ksarkies/XBee-Acquisition/Documentation/Kicad-main-sch.png

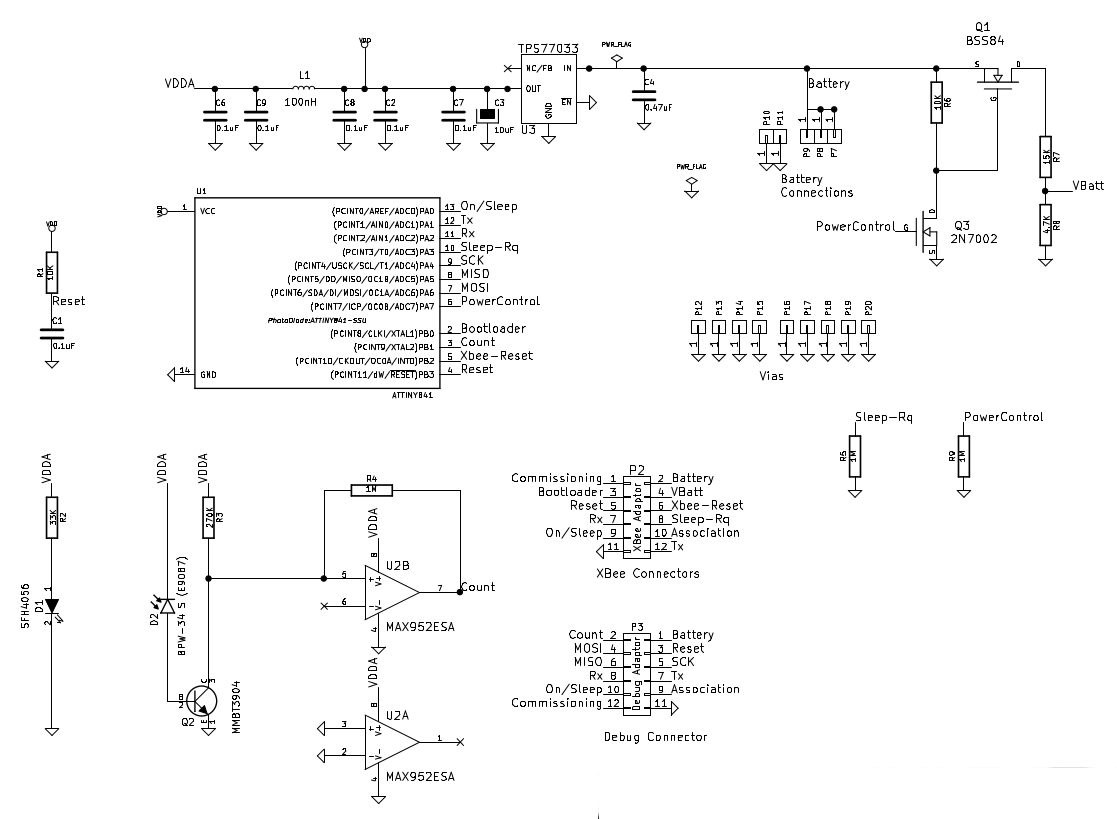
Documentation/Kicad-main-sch.png
