ksarkies/XBee-Acquisition/Documentation/Kicad-mounts-pcb-v4.png

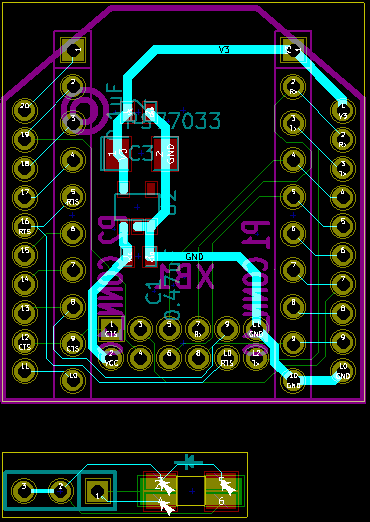
Documentation/Kicad-mounts-pcb-v4.png
