ksarkies/XBee-Acquisition/Documentation/Kicad-mounts-pcb.jpg

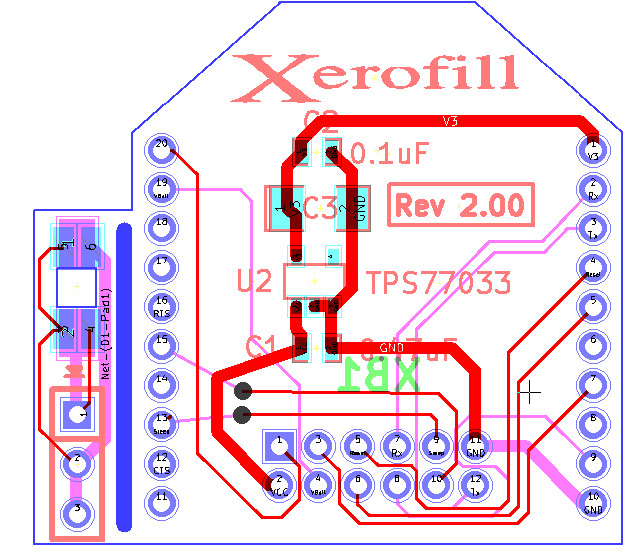
Documentation/Kicad-mounts-pcb.jpg
