ksarkies/XBee-Acquisition/Documentation/Kicad-mounts-sch.png

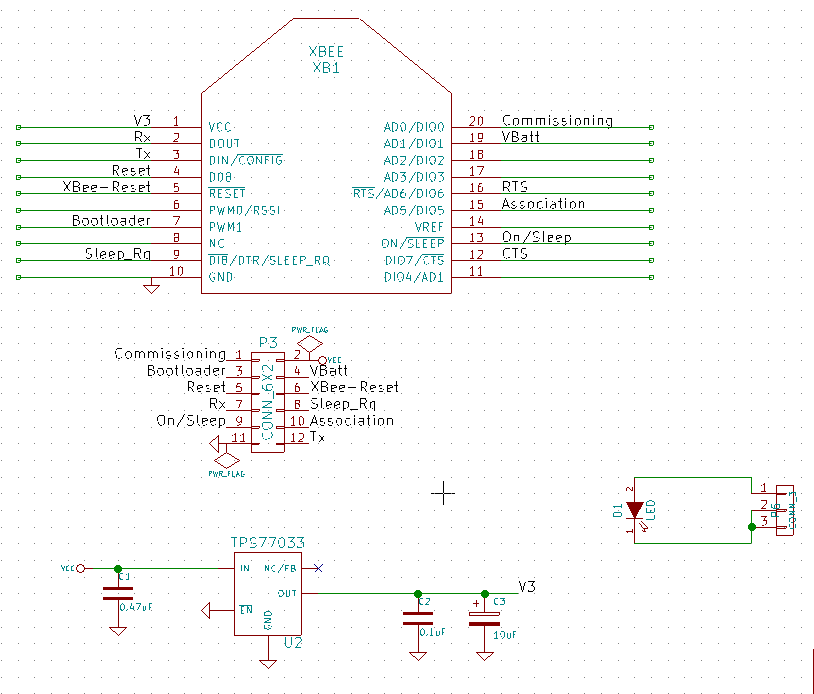
Documentation/Kicad-mounts-sch.png
