ksarkies/XBee-Acquisition/Documentation/LED-mounting-angle.jpg

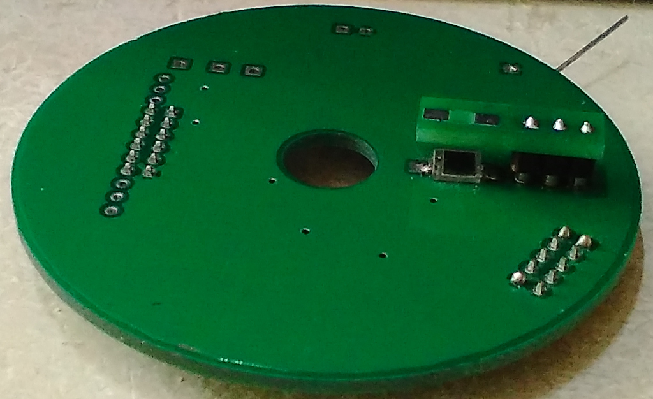
Documentation/LED-mounting-angle.jpg
