ksarkies/XBee-Acquisition/Documentation/LED-mounting-apart.jpg

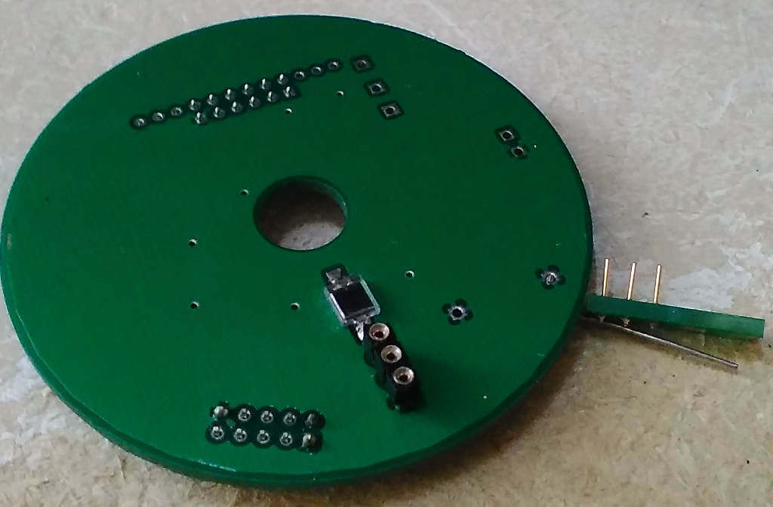
Documentation/LED-mounting-apart.jpg
