ksarkies/XBee-Acquisition/Documentation/network.png

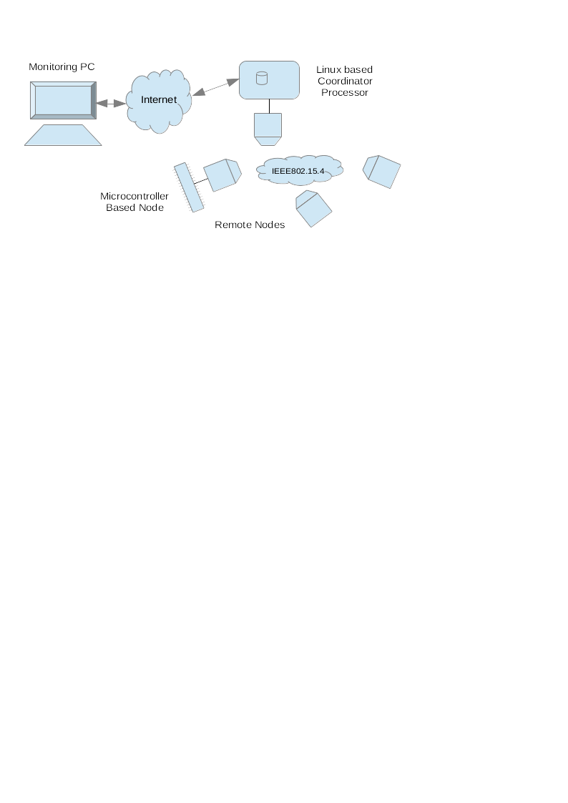
Documentation/network.png
