ksarkies/XBee-Acquisition/Documentation/Topside-of-Meter-Board-v2.jpg

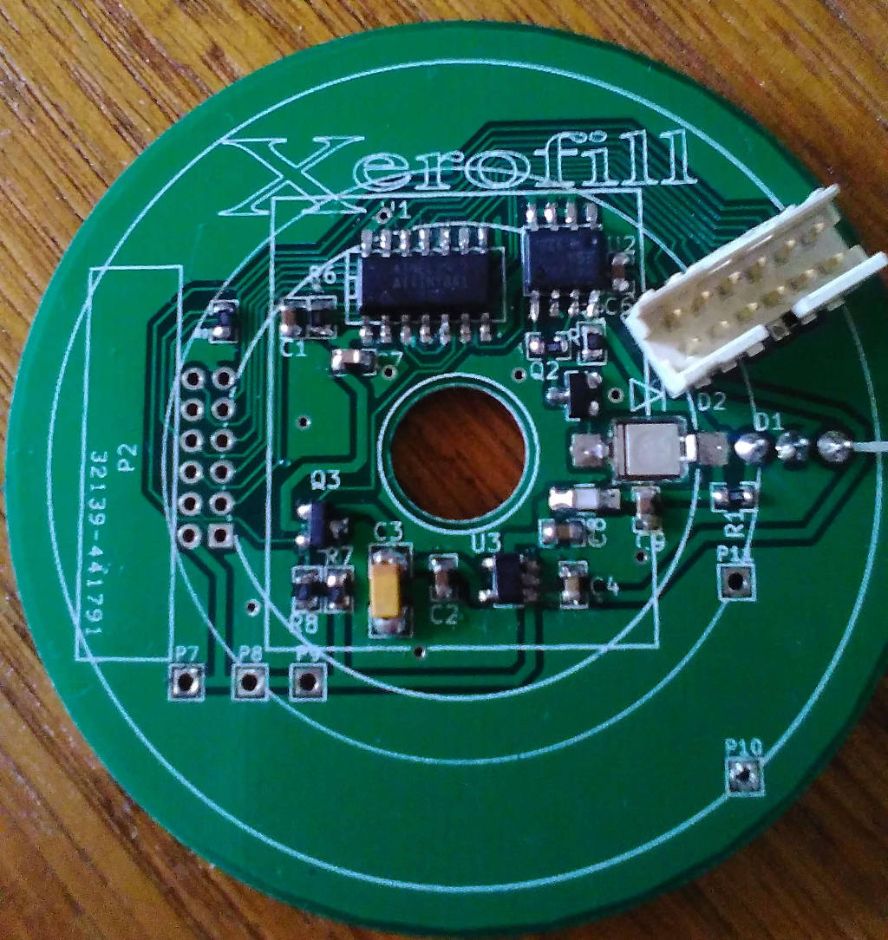
Documentation/Topside-of-Meter-Board-v2.jpg
