ksarkies/XBee-Acquisition/Documentation/Topside-of-Mounts-Board-v2.jpg

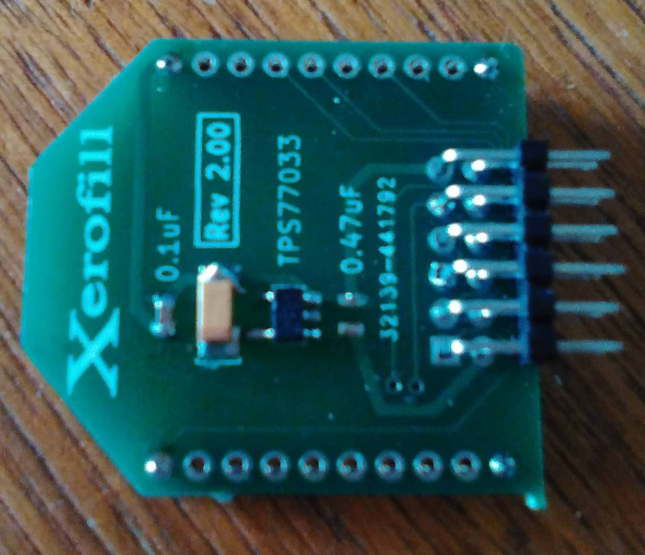
Documentation/Topside-of-Mounts-Board-v2.jpg
