ksarkies/XBee-Acquisition/Documentation/XBee-mount-bottom-view-1.jpg

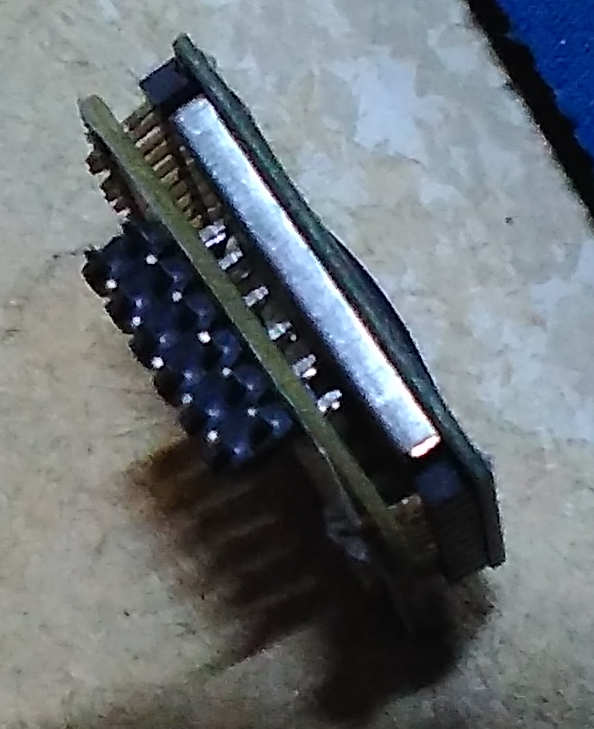
Documentation/XBee-mount-bottom-view-1.jpg
