ksarkies/XBee-Acquisition/Documentation/XBee-mount-bottom-view-2.jpg

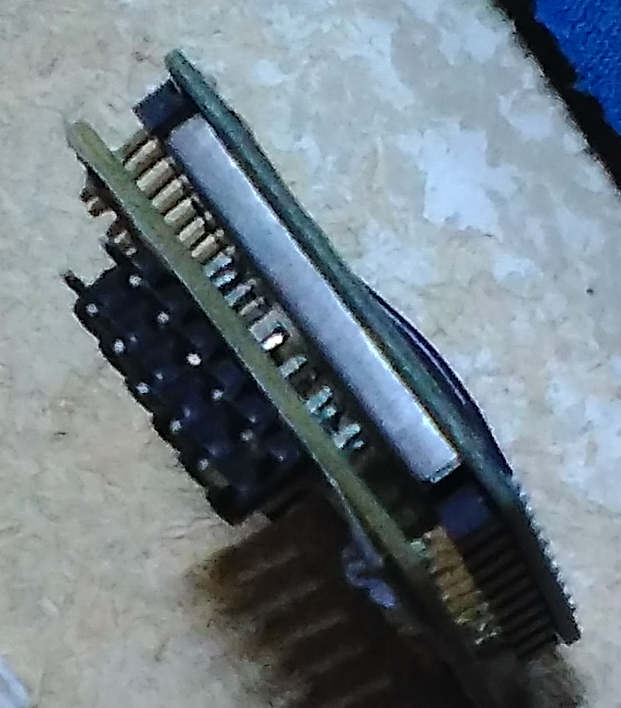
Documentation/XBee-mount-bottom-view-2.jpg
