ksarkies/XBee-Acquisition/Documentation/XBee-mount-side-view.jpg

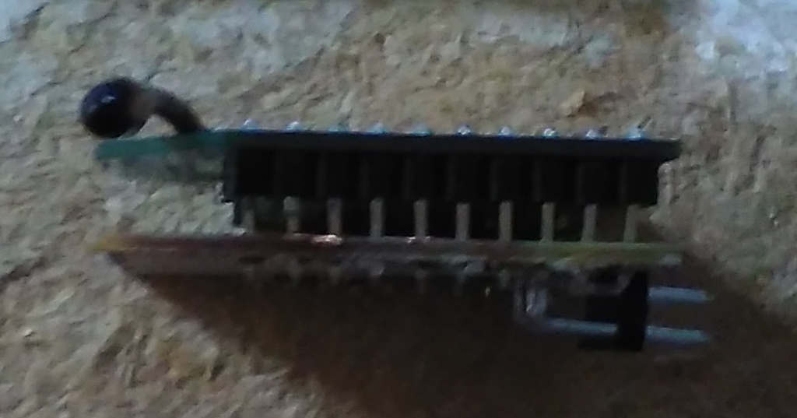
Documentation/XBee-mount-side-view.jpg
