ksarkies/XBee-Acquisition/Development/gEDA-XBee-node-test/xbee-node-atmega48.png

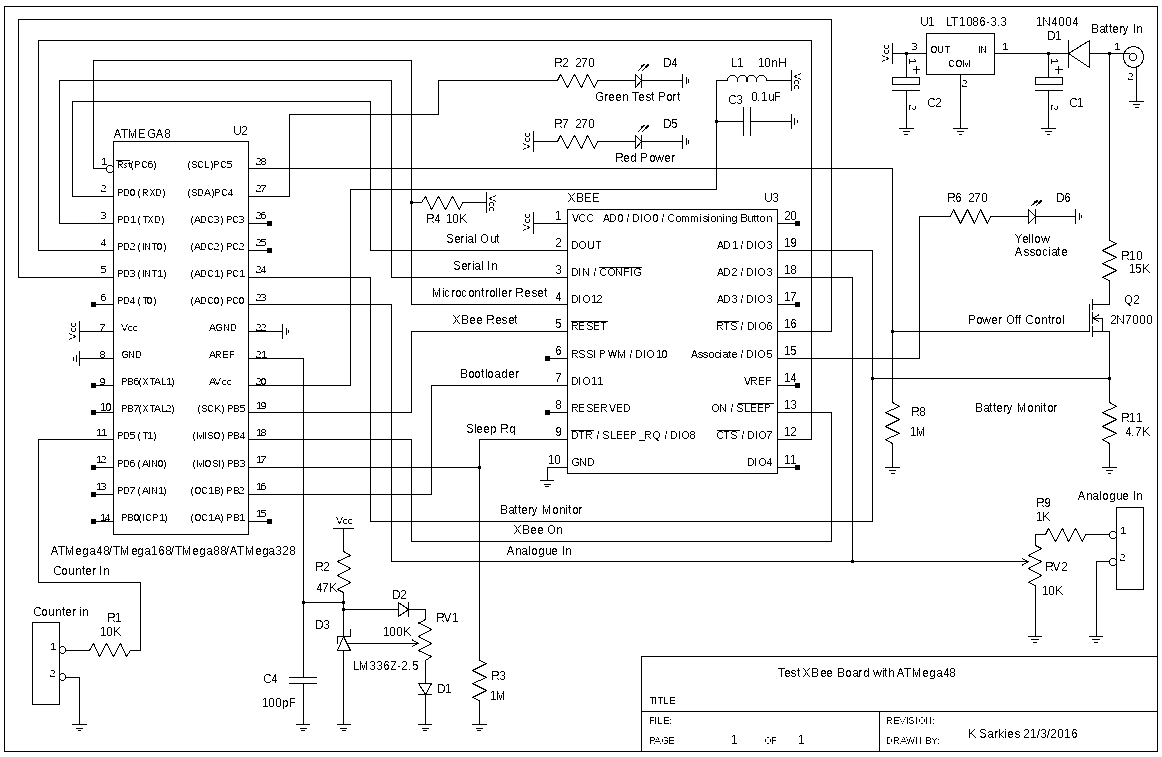
Development/gEDA-XBee-node-test/xbee-node-atmega48.png
