ksarkies/XBee-Acquisition/Development/gEDA-XBee-node-test/xbee-node-attiny4313.png

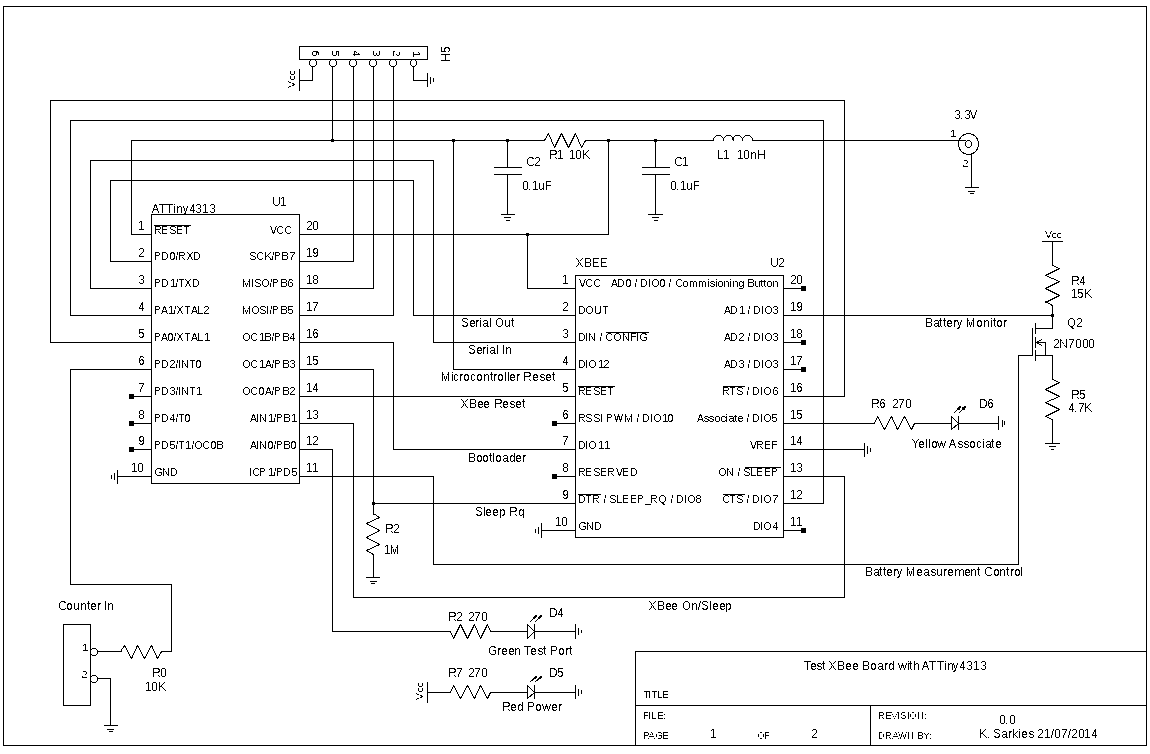
Development/gEDA-XBee-node-test/xbee-node-attiny4313.png
