ksarkies/XBee-Acquisition/Development/gEDA-XBee-node-test/xbee-node-serial.png

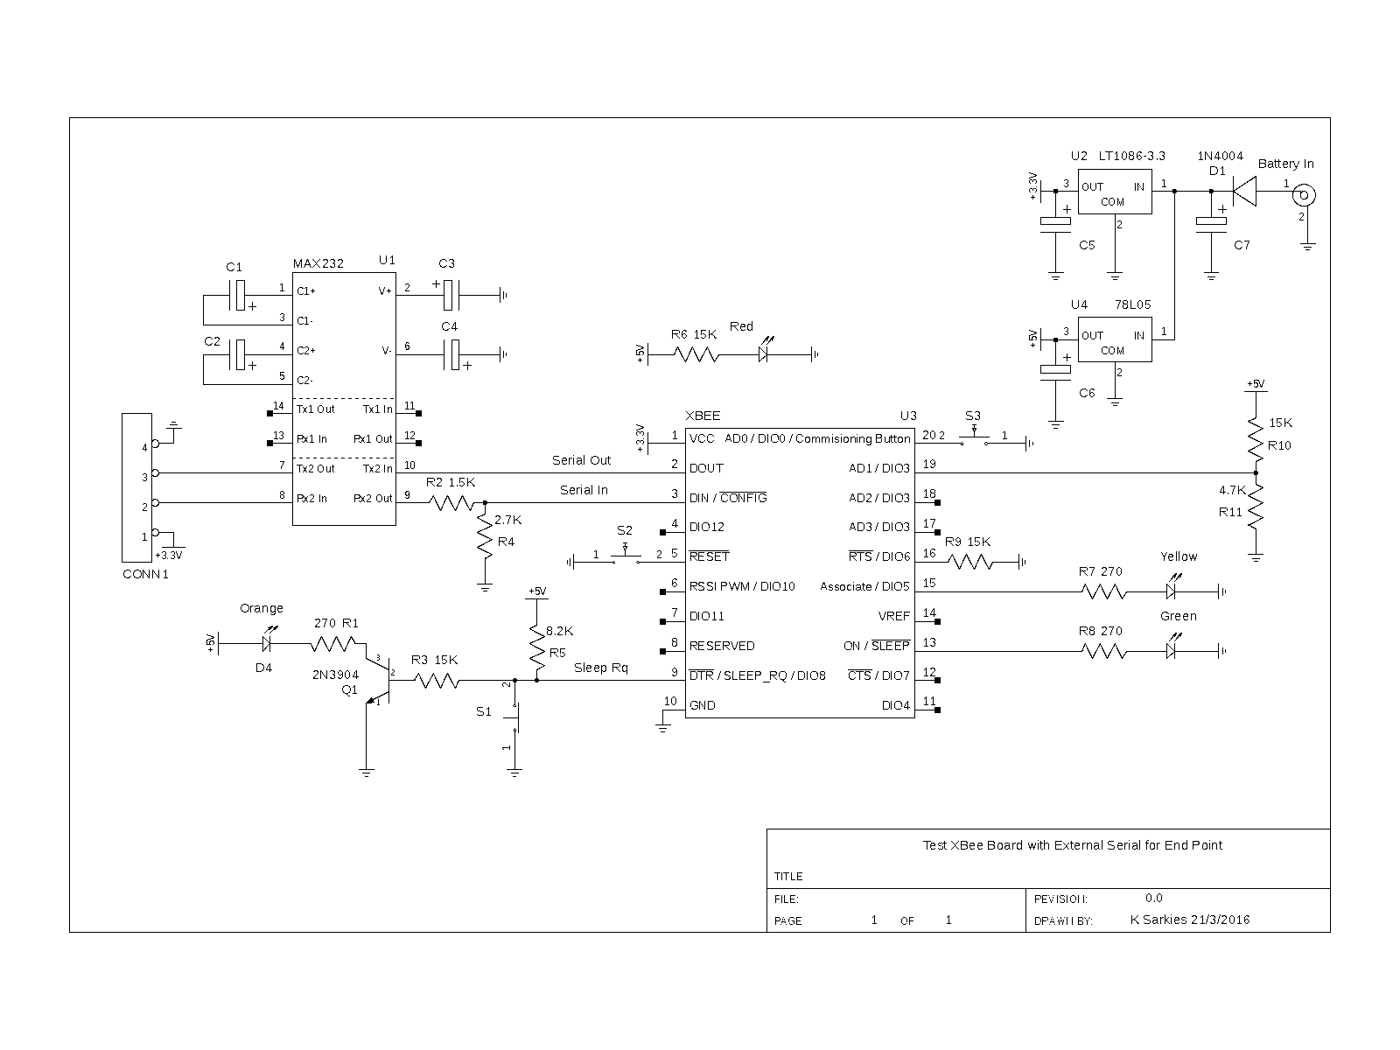
Development/gEDA-XBee-node-test/xbee-node-serial.png
