ksarkies/XBee-Acquisition/Development/Kicad-XBee-node-test/xbee-node-test.jpg

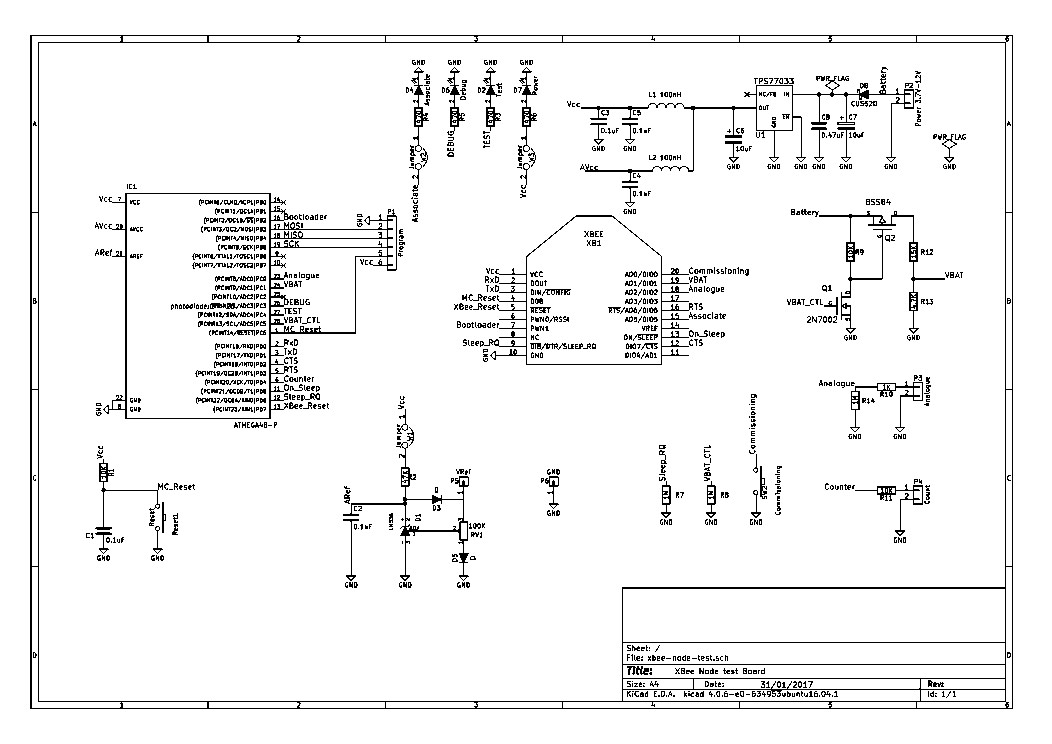
Development/Kicad-XBee-node-test/xbee-node-test.jpg
