ksarkies/XBee-Acquisition/Documentation/Kicad-TestBoard-pcb-v2.jpg

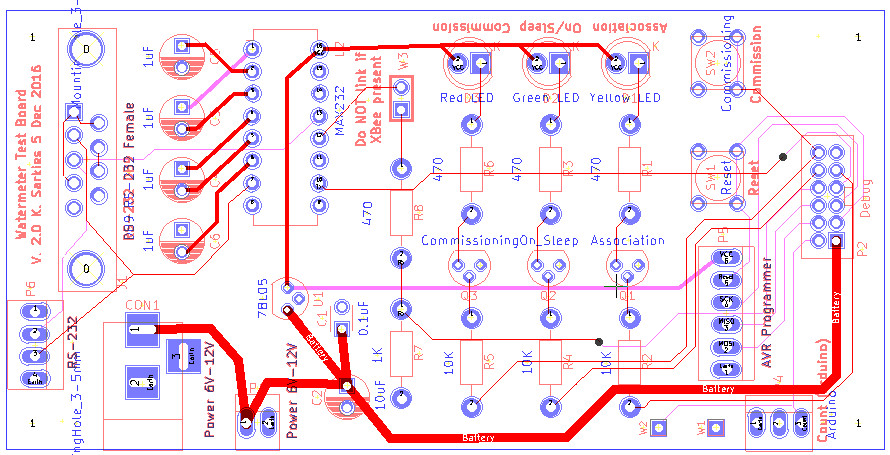
Documentation/Kicad-TestBoard-pcb-v2.jpg
