ksarkies/XBee-Acquisition/Documentation/Kicad-TestBoard-sch-v2.jpg

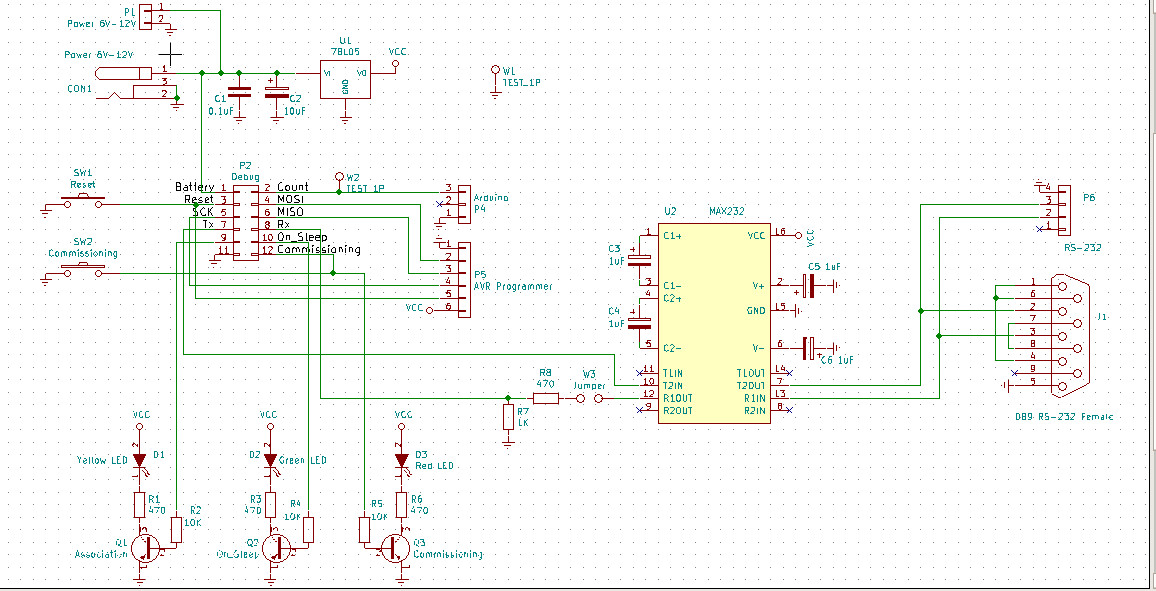
Documentation/Kicad-TestBoard-sch-v2.jpg
