ksarkies/XBee-Acquisition/Documentation/Topside-of-Testboard-v1.jpg

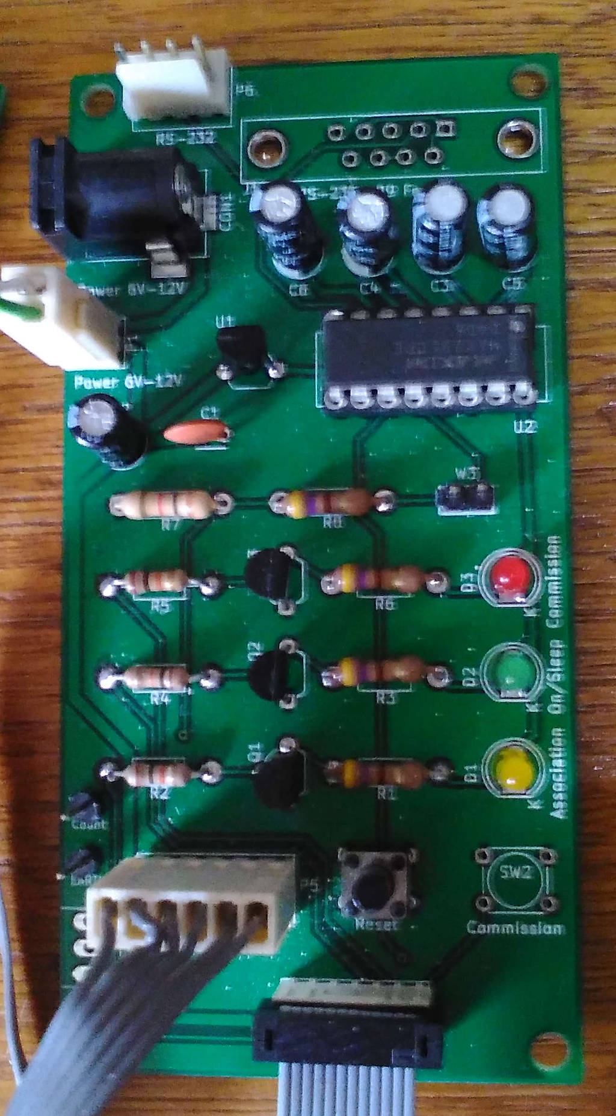
Documentation/Topside-of-Testboard-v1.jpg
