ksarkies/XBee-Acquisition/XBee-firmware/xbee-avr.c

/**
@mainpage XBee AVR Node Unit
@version 0.0.0
@author Ken Sarkies (www.jiggerjuice.info)
@date 4 January 2013
@brief Code for an AVR with an XBee in a Remote Low Power Node

This code forms the core of an interface between an XBee networking device
using ZigBee stack, and a data acquisition unit making a variety of
measurements for communication to a base controller.

@note
Software: AVR-GCC 4.5.3
@note
Target:   Any AVR with sufficient output ports and a timer
@note
Tested:   ATMega168 at 8MHz internal clock.
 */
/****************************************************************************
 *   Copyright (C) 2013 by Ken Sarkies ksarkies@internode.on.net            *
 *                                                                          *
 *   This file is part of xbee-control                                      *
 *                                                                          *
 * Licensed under the Apache License, Version 2.0 (the "License");          *
 * you may not use this file except in compliance with the License.         *
 * You may obtain a copy of the License at                                  *
 *                                                                          *
 *     http://www.apache.org/licenses/LICENSE-2.0                           *
 *                                                                          *
 * Unless required by applicable law or agreed to in writing, software      *
 * distributed under the License is distributed on an "AS IS" BASIS,        *
 * WITHOUT WARRANTIES OR CONDITIONS OF ANY KIND, either express or implied. *
 * See the License for the specific language governing permissions and      *
 * limitations under the License.                                           *
 ***************************************************************************/

#define F_CPU               8000000

#include <inttypes.h>
#include <avr/sfr_defs.h>
#include <avr/wdt.h>
#include <avr/io.h>
#include <avr/interrupt.h>
#include <avr/sleep.h>
#include <util/delay.h>
#include "serial.h"
#include "timer.h"
#include "xbee-avr.h"

/** Convenience macros (we don't use them all) */
#define TRUE 1
#define FALSE 0

#define inb(sfr) _SFR_BYTE(sfr)
#define inw(sfr) _SFR_WORD(sfr)
#define outb(sfr, val) (_SFR_BYTE(sfr) = (val))
#define outw(sfr, val) (_SFR_WORD(sfr) = (val))
#define cbi(sfr, bit) (_SFR_BYTE(sfr) &= ~_BV(bit))
#define sbi(sfr, bit) (_SFR_BYTE(sfr) |= _BV(bit))
#define high(x) ((uint8_t) (x >> 8) & 0xFF)
#define low(x) ((uint8_t) (x & 0xFF))

/*****************************************************************************/
/** Real Time Clock Global Variable

The 32 bit time can also be accessed as four bytes. Time scale is defined in
the information block.
*/
volatile union timeUnion
{
  volatile uint32_t timeValue;
  volatile uint8_t  timeByte[4];
} time;

uint8_t counter;

/*****************************************************************************/
/* Global Variables */

/** @name UART variables */
/*@{*/
    volatile uint16_t uartInput;   /**< Character and errorcode read from uart */
    volatile uint8_t lastError;    /**< Error code for transmission back */
    volatile uint8_t checkSum;     /**< Checksum on message contents */
/*@}*/

    uint32_t timeValue;
    uint8_t messageState;           /**< Progress in message reception */
    uint8_t messageReady;           /**< Indicate that a message is ready */
    uint8_t messageError;
    uint8_t coordinatorAddress64[8];
    uint8_t coordinatorAddress16[2];
    uint8_t rxOptions;

/*****************************************************************************/
/** @brief Main Program */

int main(void)
{
    wdt_disable();                  /* Stop watchdog timer */
    hardwareInit();                 /* Initialize the processor specific hardware */
    timer0Init(0,RTC_SCALE);        /* Configure the timer */
    timeValue = 0;                  /* reset timer */
/** Initialize the UART library, pass the baudrate and avr cpu clock 
(uses the macro UART_BAUD_SELECT()). Set the baudrate to a predefined value. */
    uartInit();

/** Enable interrupts, since the UART library is interrupt controlled. */
//    sei();

/* Set the coordinator addresses. All zero 64 bit address with "unknown" 16 bit
address avoids knowing the actual address, but may cause an address discovery event. */
    for  (uint8_t i=0; i < 64; i++) coordinatorAddress64[0] = 0x00;
    coordinatorAddress16[0] = 0xFE;
    coordinatorAddress16[1] = 0xFF;
    messageState = 0;
    messageReady = FALSE;
    messageError = 0;
/* Main loop */
    for(;;)
    {
        wdt_reset();

/* Check for incoming messages */
/* The Rx message variable is re-used and must be processed before the next arrives */
        rxFrameType rxMessage;
/* Wait for data to appear */
        uint16_t inputChar = getch();
        messageError = high(inputChar);
        if (messageError != NO_DATA)
        {
/* Pull in the next character and look for message start */
/* Read in the length (16 bits) and frametype then the rest to a buffer */
            uint8_t inputValue = low(inputChar);
            switch(messageState)
            {
/* Sync character */
                case 0:
                    if (inputChar == 0x7E) messageState++;
                    break;
/* Two byte length */
                case 1:
                    rxMessage.length = (inputChar << 8);
                    messageState++;
                    break;
                case 2:
                    rxMessage.length += inputValue;
                    messageState++;
                    break;
/* Frame type */
                case 3:
                    rxMessage.frameType = inputValue;
                    rxMessage.checksum = inputValue;
                    messageState++;
                    break;
/* Rest of message, maybe include addresses or just data */
                default:
                    if (messageState > rxMessage.length + 3) messageError = STATE_MACHINE;
                    else if (rxMessage.length + 3 > messageState)
                    {
                        rxMessage.message.array[messageState-4] = inputValue;
                        messageState++;
                        rxMessage.checksum += inputValue;
                    }
                    else
                    {
                        messageReady = TRUE;
                        messageState = 0;
                        if (((rxMessage.checksum + inputValue + 1) & 0xFF) > 0) messageError = CHECKSUM;
                    }
            }
        }
/* The frame types we are handling are 0x90 Rx packet and 0x8B Tx status */
        if (messageReady)
        {
            messageReady = FALSE;
            if (messageError > 0) sendch(messageError);
            else if (rxMessage.frameType == RX_REQUEST)
            {
                if (rxMessage.message.rxRequest.data[0] == 'L') cbi(PORTB,0);
                if (rxMessage.message.rxRequest.data[0] == 'O') sbi(PORTB,0);
                sendTxRequestFrame(rxMessage.message.rxRequest.sourceAddress64,
                                   rxMessage.message.rxRequest.sourceAddress16,
                                   0, 0, rxMessage.length-12, rxMessage.message.rxRequest.data);
            }
        }
    }
}

/****************************************************************************/
/** @brief Build and transmit a basic frame

Send preamble, then data block, followed by computed checksum
*/
void sendBaseFrame(txFrameType txMessage)
{
    sendch(0x7E);
    sendch(high(txMessage.length));
    sendch(low(txMessage.length));
    sendch(txMessage.frameType);
    txMessage.checksum = txMessage.frameType;
    for (uint8_t i=0; i < txMessage.length-1; i++)
    {
        uint8_t txData = txMessage.message.array[i];
        sendch(txData);
        txMessage.checksum += txData;
    }
    sendch(0xFF-txMessage.checksum);
}

/****************************************************************************/
/** @brief Build and transmit a Tx Request frame

*/
void sendTxRequestFrame(uint8_t sourceAddress64[], uint8_t sourceAddress16[],
                         uint8_t radius, uint8_t options, uint8_t dataLength, uint8_t data[])
{
    txFrameType txMessage;
    txMessage.frameType = TX_REQUEST;
    txMessage.message.txRequest.frameID = 0x02;
    txMessage.length = dataLength+14;
    for (uint8_t i=0; i < 8; i++)
    {
        txMessage.message.txRequest.sourceAddress64[i] = sourceAddress64[i];
    }
    for (uint8_t i=0; i < 2; i++)
    {
        txMessage.message.txRequest.sourceAddress16[i] = sourceAddress16[i];
    }
    txMessage.message.txRequest.radius = 0;
    txMessage.message.txRequest.options = 0;
    for (uint8_t i=0; i < dataLength; i++)
    {
        txMessage.message.txRequest.data[i] = data[i];
    }
    sendBaseFrame(txMessage);
}

/****************************************************************************/
/** @brief Initialize the hardware for process measurement

*/
void hardwareInit(void)
{
    sbi(DDRB,0);
    sbi(PORTB,0);
}

/****************************************************************************/
/** @brief Initialise the timer

*/
void timerInit(void)
{
}

/****************************************************************************/
/** @brief Initialise the timer

*/
void resetTimer(void)
{
}

/****************************************************************************/
/** @brief Timer 0 ISR.

This ISR sends a dummy data record to the coordinator.
*/

ISR(SIG_OVERFLOW0)
{
    uint8_t data[7] = "DHello";
    time.timeValue++;
    counter--;
    if (counter == 0)
    {
        sendTxRequestFrame(coordinatorAddress64, coordinatorAddress16,0,0,6,data);
    }
}
/****************************************************************************/
/**
    @brief   Initialise Timer 0

This function will initialise the timer with the mode of operation and the
clock rate to be used. An error will be returned if the timer is busy.

Because ATMega64, ATMega128, ATMega103 offer different scale factors, there
needs to be a conversion provided between the specification here and the scale
setting. The additional clock settings provided for those MCUs are not used
here, nor are the external clock settings of the remaining MCUs.

Timer 0 is typically an 8-bit timer and has very basic functionality. Some MCUs
offer PWM capability while most do not.

    @param  mode
            Ignored for simple timers.
    @param  timerClock
            00  Stopped
            01  F_CLK
            02  F_CLK/8
            03  F_CLK/64
            04  F_CLK/256
            05  F_CLK/1024

The timer continues to run until it is stopped by calling this function with
timerClock=0. At the moment, mode does nothing.
*/

void timer0Init(uint8_t mode,uint16_t timerClock)
{
  if (timerClock > 5) timerClock = 5;
#if defined(__AVR_ATMega64__) || \
    defined(__AVR_ATMega128__) || \
    defined(__AVR_ATMega103)
/* Rescale clock values to match those of the above MCUs */
  if (timerClock > 2) ++timerClock;
  if (timerClock > 4) ++timerClock;
#endif
  outb(TIMER_CONT_REG0,((inb(TIMER_CONT_REG0) & 0xF8)|(timerClock & 0x07)));
#if defined (TCNT0L)
  outw(TCNT0,0);                    /* 16 bit - clear both registers */
#else
  outb(TCNT0,0);                    /* Clear the register */
#endif
#if (TIMER_INTERRUPT_MODE == 1)
  sbi(TIMER_FLAG_REG0, TOV0);       /* Force clear the interrupt flag */
  sbi(TIMER_MASK_REG0, TOIE0);      /* Enable the overflow interrupt */
  sei();
#endif
}

/****************************************************************************/
/**
    @brief   Read Timer 0

This function will return the current timer value as a 16 bit unsigned integer
even if the timer is only 8 bit. This allows for a possibility of a 16 bit
timer being at timer 0 (so far this is not the case in any MCU).

In the event of a 16 bit register, the hardware registers must be accessed
high byte first. The avr-gcc compiler does this automatically.

    @return Timer Value.
*/

uint16_t timer0Read()
{
#if defined (TCNT0L)
  return inw(TCNT0);
#else
  return (int16_t) inb(TCNT0);
#endif
}

/****************************************************************************/
